alegoldstein/ce346-spring-2026/Firmware/ESP/CE346_ESP/src/init.h

//all pin definitinos except leds
#define PDM_DATA    26
#define PDM_CLK     27
#define BCLK        14
#define LRCL        13
#define SPI_MISO    23
#define SPI_MOSI    19
#define SPI_CS      5
#define SPI_SCK     18
#define DOUT        22
#define UART2_TX    21
#define UART2_RX    34
#define GAME_BTN    35
#define SOUND_BTN   39 //VN
#define KILL_BTN    36 //VP


void init_uart(void);

void init_spi(void);

void init_scoreboard();
